opatiny/stea-mp-unk-3/pictures/testDefine.png

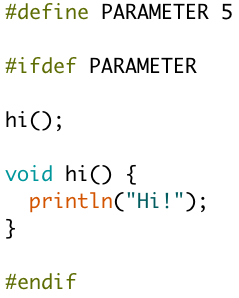
pictures/testDefine.png
