opatiny/stea-mp-unk-3/arduino/cardReader/returnTemperature/returnTemperature.ino

#include <OneWire.h>

OneWire  ds(5);  // on pin 10 (a 4.7K resistor is necessary)

void setup(void) {
  Serial.begin(9600);
}

void loop(void) {
  byte i;
  byte present = 0;
  byte data[12];
  byte addr[8];
  float celsius;

  if ( !ds.search(addr)) {
    Serial.println();
    ds.reset_search();
    delay(250);
    return;
  }


  ds.reset();
  ds.select(addr);
  ds.write(0x44, 1);        // start conversion, with parasite power on at the end

  delay(1000);

  present = ds.reset();
  ds.select(addr);
  ds.write(0xBE);         // Read Scratchpad

  for ( i = 0; i < 9; i++) {           // we need 9 bytes
    data[i] = ds.read();
  }


  if (OneWire::crc8(data, 8) == data[8]) {
    Serial.println("Check digit passed.");
  }


  // Convert the data to actual temperature
  int16_t raw = (data[1] << 8) | data[0];

  byte cfg = (data[4] & 0x60);
  // at lower res, the low bits are undefined, so let's zero them
  if (cfg == 0x00) raw = raw & ~7;  // 9 bit resolution, 93.75 ms
  else if (cfg == 0x20) raw = raw & ~3; // 10 bit res, 187.5 ms
  else if (cfg == 0x40) raw = raw & ~1; // 11 bit res, 375 ms
  //// default is 12 bit resolution, 750 ms conversion time


  celsius = (float)raw / 16.0;
  Serial.print("  Temperature = ");
  Serial.print(celsius);
  Serial.println(" Celsius");

}
