opatiny/stea-mp-unk-3/arduino/ledDisplay/driverOnOff/driverOnOff.ino

/*****************
Based on PCA9685 library example (BasicLEDTest)
Blinks all segments on and off
*/

#include <Wire.h>
#include <PCA9685.h>


PCA9685 ledDriver;

void setup()
{
  Serial.begin(9600); // set up serial
  Serial.println("Serial Started");

  Wire.begin();           // Wire must be started!
  ledDriver.begin(B000000);  // Address pins A5-A0 set to B111000
  ledDriver.init();

}

void loop() {

  for (int i = 0; i < 16; i++)  {
    ledDriver.setLEDOn(i);
    //delay(5);
  }
  for (int i = 0; i < 16; i++)  {
    ledDriver.setLEDOff(i);
    //delay(5);
  }
}
